mkgeiger/matrix-weather-clock/MatrixWeatherClock/icons.c

#include "icons.h"

const uint8_t icon1d[ICON_WIDTH * ICON_HEIGHT] PROGMEM = {
		0, 0, 4, 4, 0, 0, 2, 2, 0,
		0, 4, 4, 4, 4, 2, 2, 2, 2,
		4, 4, 4, 4, 4, 4, 4, 2, 2,
		4, 4, 4, 4, 4, 4, 4, 4, 4,
		0, 4, 2, 2, 4, 3, 4, 4, 3,
		0, 0, 2, 4, 4, 3, 4, 3, 0,
		0, 2, 2, 0, 3, 0, 0, 3, 0,
		0, 2, 0, 0, 3, 0, 3, 0, 0,
		2, 0, 0, 3, 0, 0, 0, 0, 0
};

const uint8_t icon1n[ICON_WIDTH * ICON_HEIGHT] PROGMEM = {
		0, 0, 4, 4, 0, 0, 5, 5, 0,
		0, 4, 4, 4, 4, 5, 5, 5, 5,
		4, 4, 4, 4, 4, 4, 4, 5, 5,
		4, 4, 4, 4, 4, 4, 4, 4, 4,
		0, 4, 2, 2, 4, 3, 4, 4, 3,
		0, 0, 2, 4, 4, 3, 4, 3, 0,
		0, 2, 2, 0, 3, 0, 0, 3, 0,
		0, 2, 0, 0, 3, 0, 3, 0, 0,
		2, 0, 0, 3, 0, 0, 0, 0, 0
};

const uint8_t icon2[ICON_WIDTH * ICON_HEIGHT] PROGMEM = {
		0, 0, 0, 0, 0, 0, 0, 0, 2,
		0, 0, 0, 2, 2, 0, 0, 2, 0,
		0, 0, 2, 2, 0, 0, 2, 0, 0,
		0, 2, 2, 0, 0, 2, 2, 2, 2,
		2, 2, 2, 2, 0, 0, 0, 2, 0,
		0, 0, 2, 0, 0, 0, 2, 0, 0,
		0, 2, 0, 0, 0, 0, 0, 0, 0,
		2, 0, 0, 0, 0, 0, 0, 0, 0,
		0, 0, 0, 0, 0, 0, 0, 0, 0
};

const uint8_t icon3d[ICON_WIDTH * ICON_HEIGHT] PROGMEM = {
		0, 0, 4, 4, 0, 0, 2, 2, 0,
		0, 4, 4, 4, 4, 2, 2, 2, 2,
		4, 3, 3, 4, 3, 3, 4, 2, 2,
		4, 3, 3, 4, 3, 3, 4, 4, 4,
		0, 4, 4, 4, 4, 4, 4, 4, 4,
		0, 0, 4, 4, 4, 3, 3, 0, 0,
		0, 0, 0, 0, 0, 3, 3, 0, 0,
		0, 0, 0, 0, 0, 0, 0, 0, 0,
		0, 0, 0, 0, 0, 0, 0, 0, 0
};

const uint8_t icon3n[ICON_WIDTH * ICON_HEIGHT] PROGMEM = {
		0, 0, 4, 4, 0, 0, 5, 5, 0,
		0, 4, 4, 4, 4, 5, 5, 5, 5,
		4, 3, 3, 4, 3, 3, 4, 5, 5,
		4, 3, 3, 4, 3, 3, 4, 4, 4,
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
		0, 0, 0, 0, 0, 0, 0, 0, 0,
		0, 0, 0, 0, 0, 0, 0, 0, 0,
		0, 4, 4, 4, 4, 4, 4, 0, 0,
		0, 0, 0, 0, 0, 0, 0, 0, 0,
		4, 4, 4, 4, 4, 4, 0, 4, 4,
		0, 0, 0, 0, 0, 0, 0, 0, 0,
		0, 0, 4, 4, 4, 4, 4, 4, 0,
		0, 0, 0, 0, 0, 0, 0, 0, 0,
		0, 0, 0, 0, 0, 0, 0, 0, 0
};

const uint8_t icon23d[ICON_WIDTH * ICON_HEIGHT] PROGMEM = {
		0, 0, 4, 4, 0, 0, 2, 2, 0,
		0, 4, 4, 4, 4, 2, 2, 2, 2,
		4, 4, 4, 4, 4, 4, 4, 2, 2,
		4, 4, 4, 4, 4, 4, 4, 4, 4,
		0, 4, 4, 3, 4, 3, 4, 4, 3,
		0, 0, 3, 4, 4, 3, 4, 3, 0,
		0, 0, 0, 0, 3, 0, 0, 0, 0,
		0, 3, 0, 0, 0, 0, 3, 0, 0,
		0, 0, 0, 3, 0, 0, 0, 0, 0
};

const uint8_t icon23n[ICON_WIDTH * ICON_HEIGHT] PROGMEM = {
		0, 0, 4, 4, 0, 0, 5, 5, 0,
		0, 4, 4, 4, 4, 5, 5, 5, 5,
		4, 4, 4, 4, 4, 4, 4, 5, 5,
		4, 4, 4, 4, 4, 4, 4, 4, 4,
		0, 4, 4, 3, 4, 3, 4, 4, 3,
		0, 0, 3, 4, 4, 3, 4, 3, 0,
		0, 0, 0, 0, 3, 0, 0, 0, 0,
		0, 3, 0, 0, 0, 0, 3, 0, 0,
		0, 0, 0, 3, 0, 0, 0, 0, 0
};

const uint8_t icon24[ICON_WIDTH * ICON_HEIGHT] PROGMEM = {
		0, 0, 0, 0, 0, 0, 0, 0, 0,
		0, 0, 0, 0, 0, 0, 4, 4, 0,
		0, 0, 0, 0, 0, 0, 0, 0, 4,
		4, 4, 4, 4, 4, 4, 4, 4, 0,
		0, 0, 0, 0, 0, 0, 0, 0, 0,
		4, 4, 4, 4, 4, 4, 0, 0, 0,
		0, 0, 0, 0, 0, 0, 4, 0, 0,
		0, 0, 0, 0, 4, 4, 0, 0, 0,
		0, 0, 0, 0, 0, 0, 0, 0, 0
};

const icon_list_t icon_list[NBR_ICONS] PROGMEM = {
		// Gewitter
		{200, icon1d , icon1n }, // Gewitter mit leichtem Regen
		{201, icon1d , icon1n }, // Gewitter mit Regen
		{202, icon1d , icon1n }, // Gewitter mit starkem Regen
		{210, icon2  , icon2  }, // leichtes Gewitter
		{211, icon2  , icon2  }, // Gewitter
		{212, icon2  , icon2  }, // starkes Gewitter
		{221, icon2  , icon2  }, // phasenweises Gewitter
		{230, icon1d , icon1n }, // Gewitter mit leichtem Nieselregen
		{231, icon1d , icon1n }, // Gewitter mit Regen
		{232, icon1d , icon1n }, // Gewitter mit starkem Regen
		// Nieselregen
		{300, icon3d , icon3n }, // leichter Nieselregen
		{301, icon3d , icon3n }, // Nieselregen
		{302, icon4d , icon4n }, // starker Nieselregen
		{310, icon5d , icon5n }, // leichter Nieselregen/Regen
		{311, icon4d , icon4n }, // Nieselregen/Regen
		{312, icon4d , icon4n }, // starker Nieselregen/Regen 
		{313, icon6d , icon6n }, // Regenschauer und Nebel
		{314, icon4d , icon4n }, // starker Regenschauer und Nebel 
		{321, icon3d , icon3n }, // Regenschauer und Nieselregen
		// Regen
		{500, icon3d , icon3n }, // leichter Regen
		{501, icon4d , icon4n }, // mäßiger Regen
		{502, icon4d , icon4n }, // starker Regen
		{503, icon4d , icon4n }, // sehr starker Regen
		{504, icon4d , icon4n }, // extremer Regen
		{511, icon5d , icon5n }, // gefrierender Regen
		{520, icon6d , icon6n }, // leichter Regenschauer/Regen
		{521, icon6d , icon6n }, // Regenschauer
		{522, icon6d , icon6n }, // starker Regenschauer/Regen
		{531, icon7d , icon7n }, // phasenweise Regenschauer/Regen
		// Schnee
		{600, icon8d , icon8n }, // leichter Schneefall
		{601, icon8d , icon8n }, // Schneefall 
		{602, icon9d , icon9n }, // starker Schneefall
		{611, icon5d , icon5n }, // Schneeregen
		{612, icon5d , icon5n }, // Graupelschauer
		{615, icon5d , icon5n }, // leichter Regen und Schnee
		{616, icon5d , icon5n }, // Regen und Schnee
		{620, icon5d , icon5n }, // leichter Schneeregen
		{621, icon8d , icon8n }, // Schneeregen
		{622, icon8d , icon8n }, // starker Schneeregen
		// Atmosphäre
		{701, icon6d , icon6n }, // feiner Nebel/Dunst
		{711, icon10 , icon10 }, // Rauch
		{721 ,icon11d, icon11n}, // Dunst
		{731 ,icon12 , icon12 }, // Sand/Staubwirbel
		{741, icon13d, icon13n}, // Nebel
		{761 ,icon12 , icon12 }, // Staub
		{762 ,icon12 , icon12 }, // Vulkanasche
		{771, icon14d, icon14n}, // Wind-/Sturmböen
		{781, icon15,  icon15 }, // Tornado
		// Wolken
		{800, icon16d, icon16n}, // klarer Himmel
		{801, icon14d, icon14n}, // wenige Schleierwolken
		{802, icon14d, icon14n}, // aufgelockerte Bewölkung
		{803, icon17d, icon17n}, // bewölkt mit Aufhellungen
		{804, icon18 , icon18 }, // bewölkt
		// Extrem
		{900, icon15 , icon15 }, // Tornado
		{901, icon7d , icon7n }, // Tropensturm
		{902, icon19 , icon19 }, // Hurrikan
		{903, icon20 , icon20 }, // kalt
		{904, icon21d, icon21n}, // heiß
		{905, icon22 , icon22 }, // windig
		{906, icon23d, icon23n}, // Hagel
		// Ergänzende
		{957, icon24 , icon24 }  // starker Wind, kurz vor Sturm
};
